NikolajHC-Hydac/warehouse-label-exam/documentation/code_flow_diagram.png

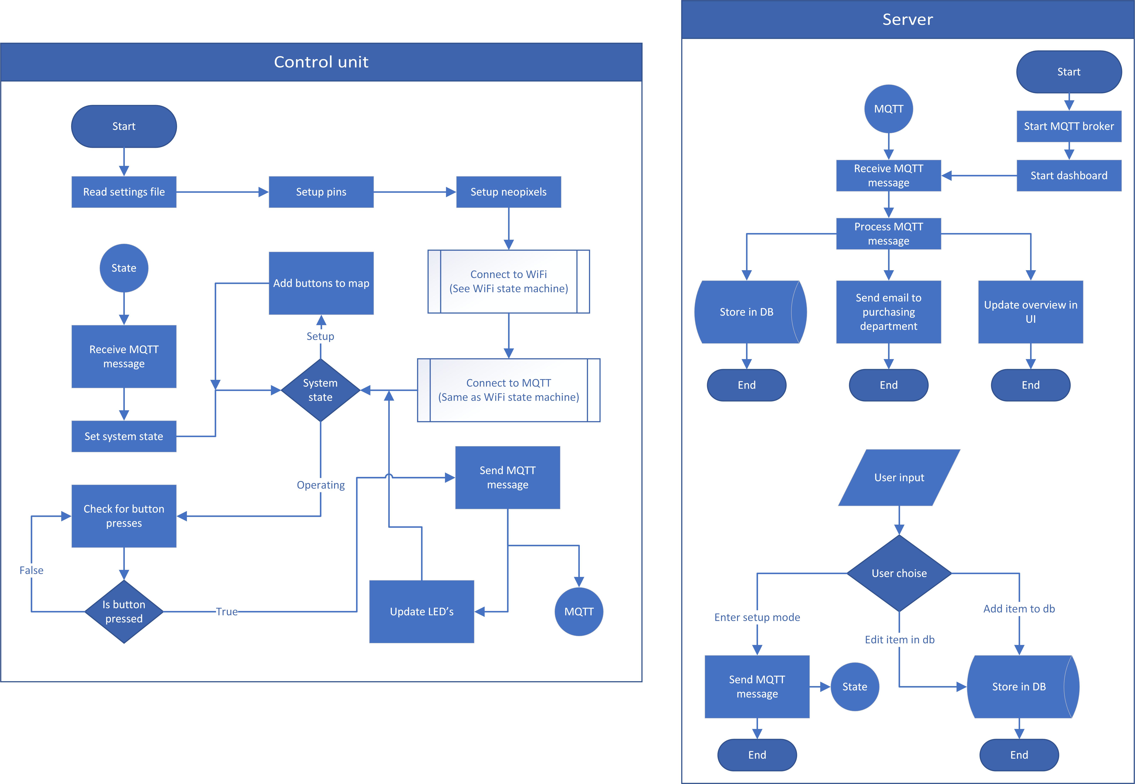
documentation/code_flow_diagram.png
