NikolajHC-Hydac/warehouse-label-exam/documentation/uml_sequence_button_press.png

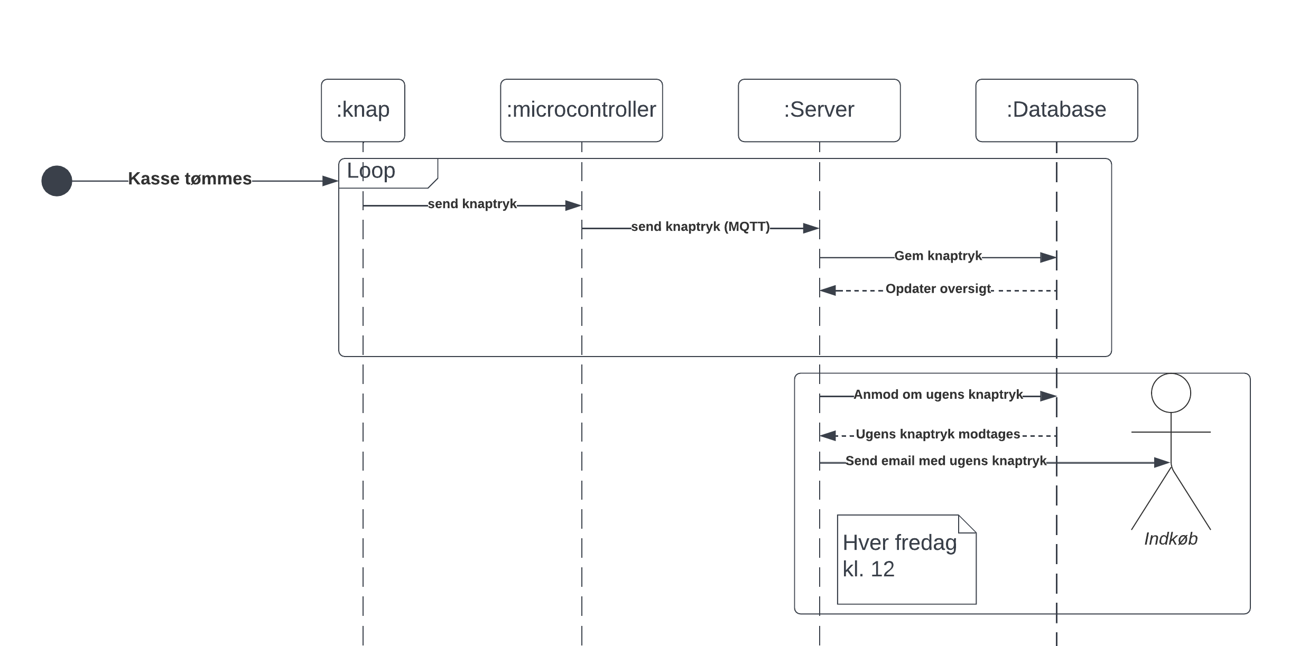
documentation/uml_sequence_button_press.png
