NikolajHC-Hydac/warehouse-label-exam/documentation/uml_use_case.png

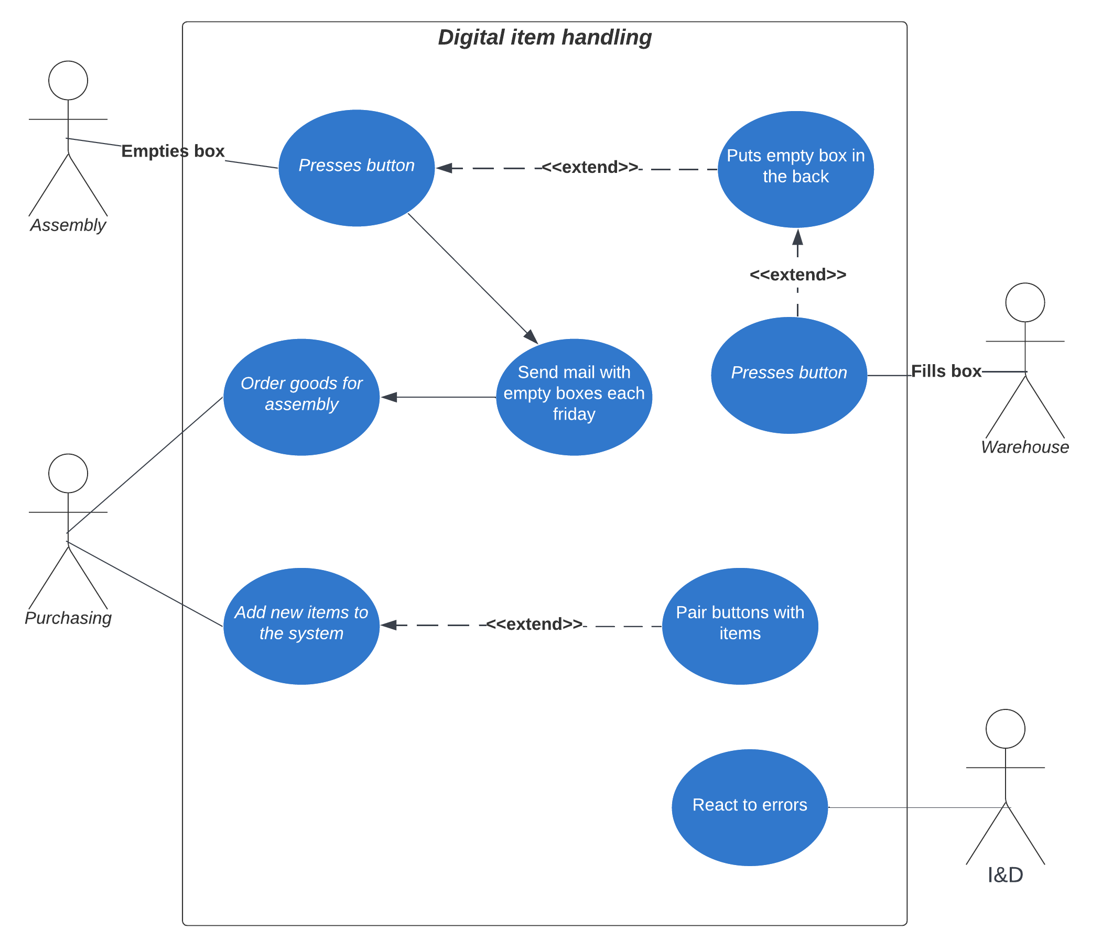
documentation/uml_use_case.png
