NikolajHC-Hydac/warehouse-label-exam/code/tests/oneWire_switch/src/main.cpp

#include <oneWire.h>

OneWire button(10);  //replace 10 with the actual pin number used
byte lastAddr[8];
byte addr[8];
byte i;

void PrintBytes(const uint8_t* addr, uint8_t count, bool newline=true) {
  for (uint8_t i = 0; i < count; i++) {
    Serial.print(addr[i]>>4, HEX);
    Serial.print(addr[i]&0x0f, HEX);
  }
  if (newline)
    Serial.println();
}

void setup() {
  Serial.begin(9600);
}

void loop() {
  if (!button.search(addr)){
    Serial.println("no more addresses");
    button.reset_search();
    delay(1000);
    return;
  }

  if (OneWire::crc8(addr, 7) != addr[7]){
    Serial.println("CRC is not valid");
    return;
  }

  uint8_t buf[13];  // Put everything in the buffer so we can compute CRC easily.
  buf[0] = 0xF0;    // Read PIO Registers
  buf[1] = 0x88;    // LSB address
  buf[2] = 0x00;    // MSB address
  button.write_bytes(buf, 3);
  button.read_bytes(buf+3, 10);     // 3 cmd bytes, 6 data bytes, 2 0xFF, 2 CRC16
  button.reset();

  if (!OneWire::check_crc16(buf, 11, &buf[11])) {
    Serial.print("CRC failure in DS2408 at ");
    PrintBytes(addr, 8, true);
    return;
  }
  Serial.print("  DS2408 data = ");
  // First 3 bytes contain command, register address.
  Serial.println(buf[3], BIN);
}
